auauuaua/go-fetch/go fetch Card Player/Resources/CardPlayer_title.png

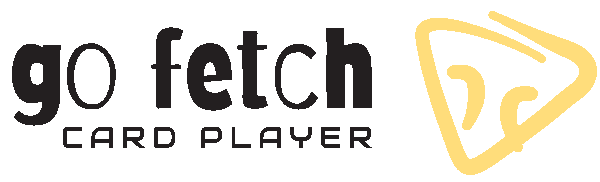
go fetch Card Player/Resources/CardPlayer_title.png
